wt29/Anemometer/stl/AnemometerRotor.stl

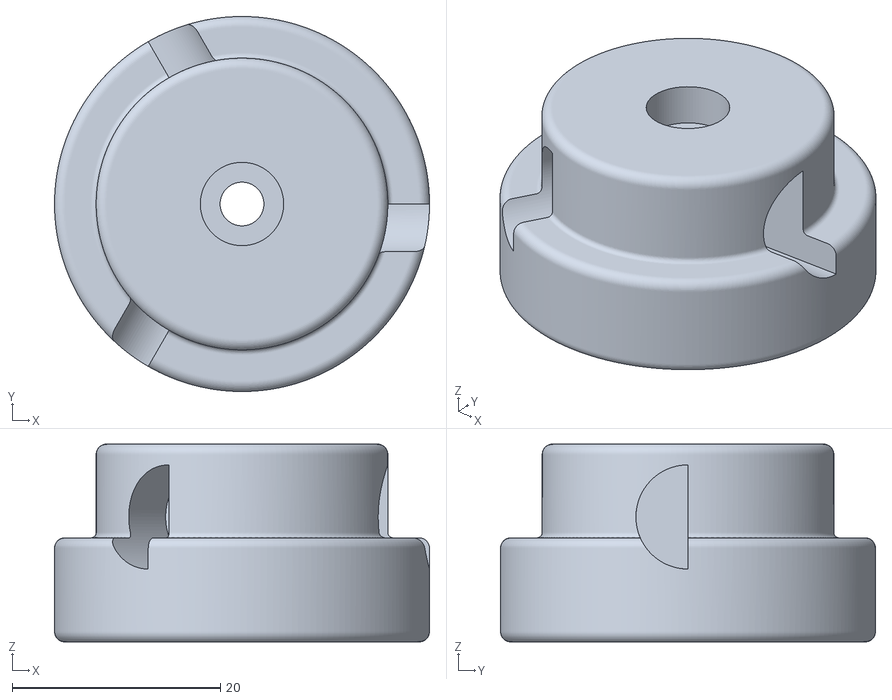
[picture p15: CAD file, 2023-05-25]
stl/AnemometerRotor.stl
36.0 x 36.0 x 19.0
