wt29/Anemometer/stl/WindVane.stl

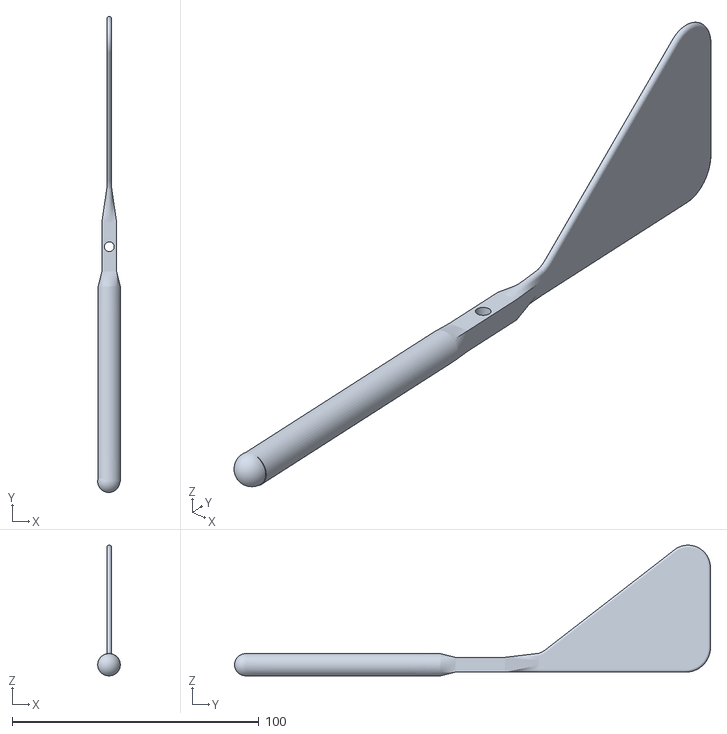
[picture p16: CAD file, 2023-05-25]
stl/WindVane.stl
9.19 x 192.9 x 52.9
