wt29/Anemometer/stl/RG_Frame.stl

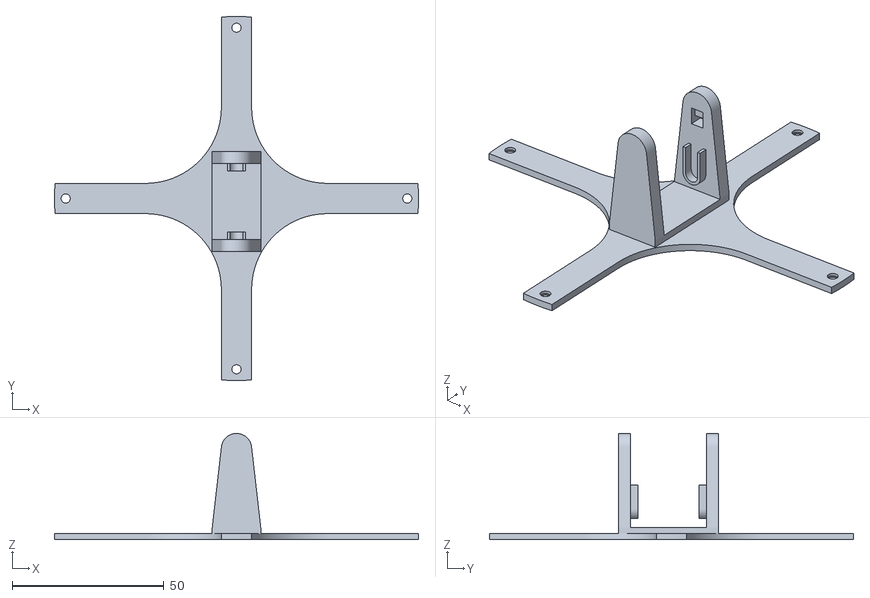
[picture p17: CAD file, 2023-05-25]
stl/RG_Frame.stl
120.0 x 120.0 x 35.0
