wt29/Anemometer/stl/AnemometerRotorCap.stl

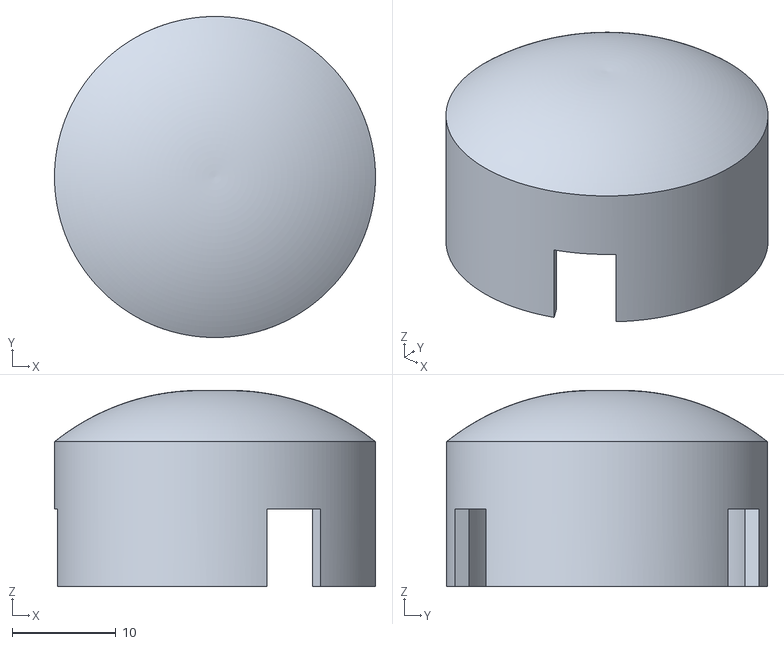
[picture p18: CAD file, 2023-05-25]
stl/AnemometerRotorCap.stl
31.0 x 31.0 x 19.0
