wt29/Anemometer/stl/Lid.stl

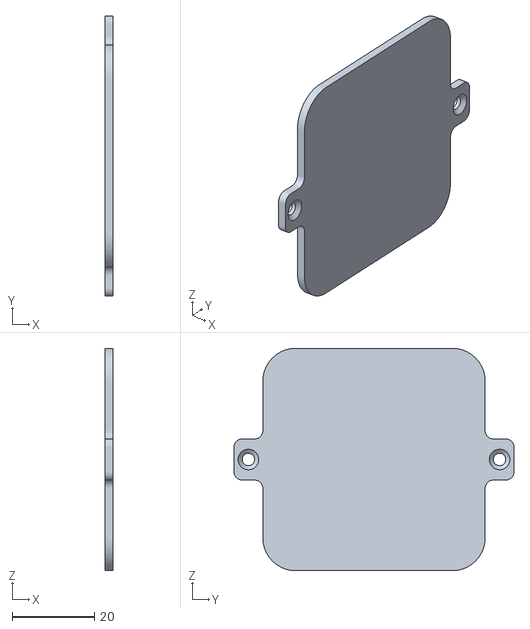
[picture p19: CAD file, 2023-05-25]
stl/Lid.stl
2.00 x 68.0 x 54.0
